aaravjhamb/zhifubao/assets/41279.jpg

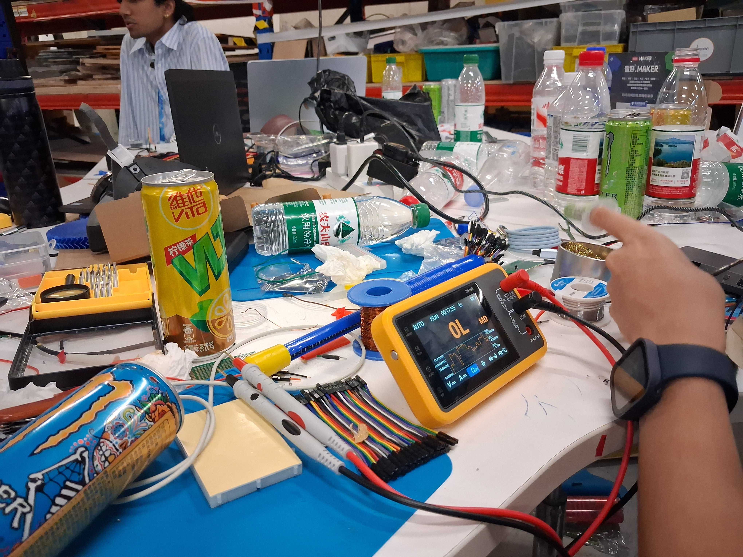
assets/41279.jpg
