aaravjhamb/zhifubao/hardware/zhifubros.kicad_sch

## KiCad design hardware/zhifubros.kicad_sch (2026-07-06, an earlier design)

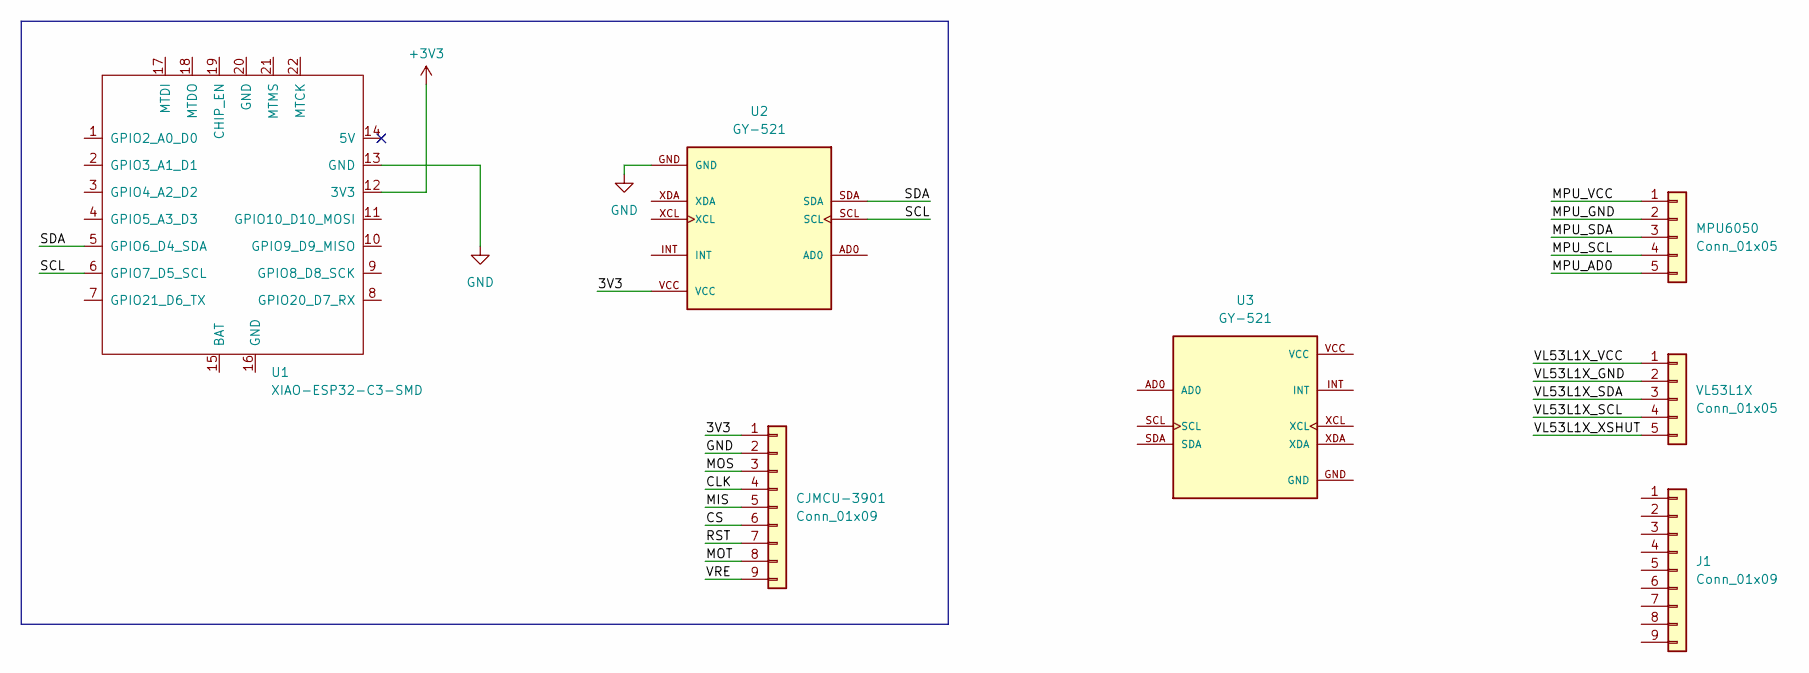
[picture p15: schematic zhifubros.kicad_sch]

Parts:
CJMCU-3901: Conn_01x09
J1: Conn_01x09
MPU6050: Conn_01x05
U1: XIAO-ESP32-C3-SMD
U2, U3: GY-521; MODULE_GY-521; PARTREV NA
VL53L1X: Conn_01x05

Connections:
3V3: CJMCU-3901.1, U2.VCC
+3V3: U1.12 (3V3)
CLK: CJMCU-3901.4
CS: CJMCU-3901.6
GND: CJMCU-3901.2, U1.13 (GND), U2.GND
MIS: CJMCU-3901.5
MOS: CJMCU-3901.3
MOT: CJMCU-3901.8
MPU_AD0: MPU6050.5
MPU_GND: MPU6050.2
MPU_SCL: MPU6050.4
MPU_SDA: MPU6050.3
MPU_VCC: MPU6050.1
RST: CJMCU-3901.7
SCL: U1.6 (GPIO7_D5_SCL), U2.SCL
SDA: U1.5 (GPIO6_D4_SDA), U2.SDA
VL53L1X_GND: VL53L1X.2
VL53L1X_SCL: VL53L1X.4
VL53L1X_SDA: VL53L1X.3
VL53L1X_VCC: VL53L1X.1
VL53L1X_XSHUT: VL53L1X.5
VRE: CJMCU-3901.9
