aaravjhamb/zhifubao/assets/41325.jpg

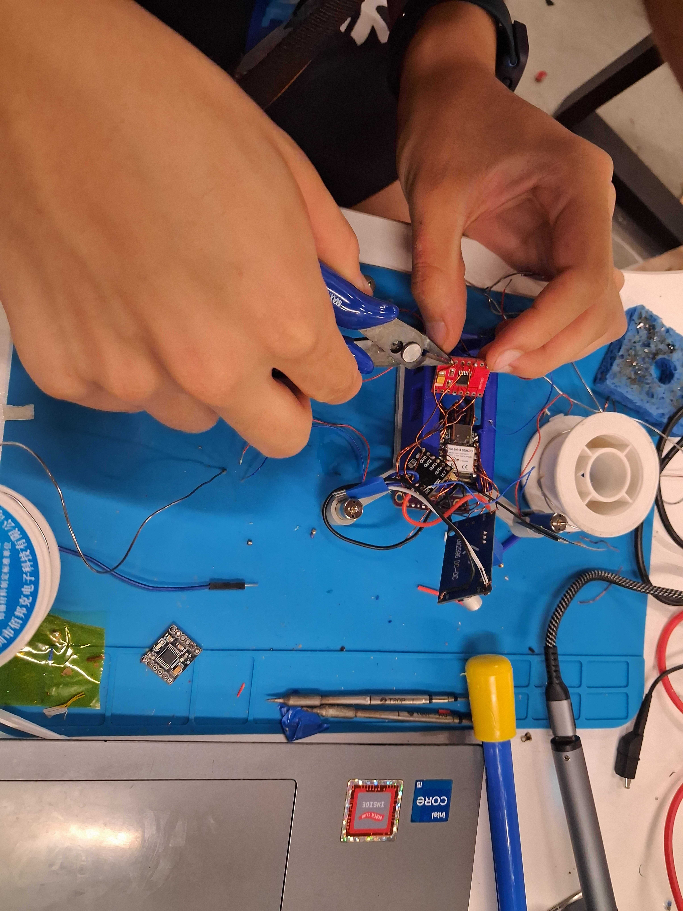
assets/41325.jpg
