aaravjhamb/zhifubao/assets/41326.jpg

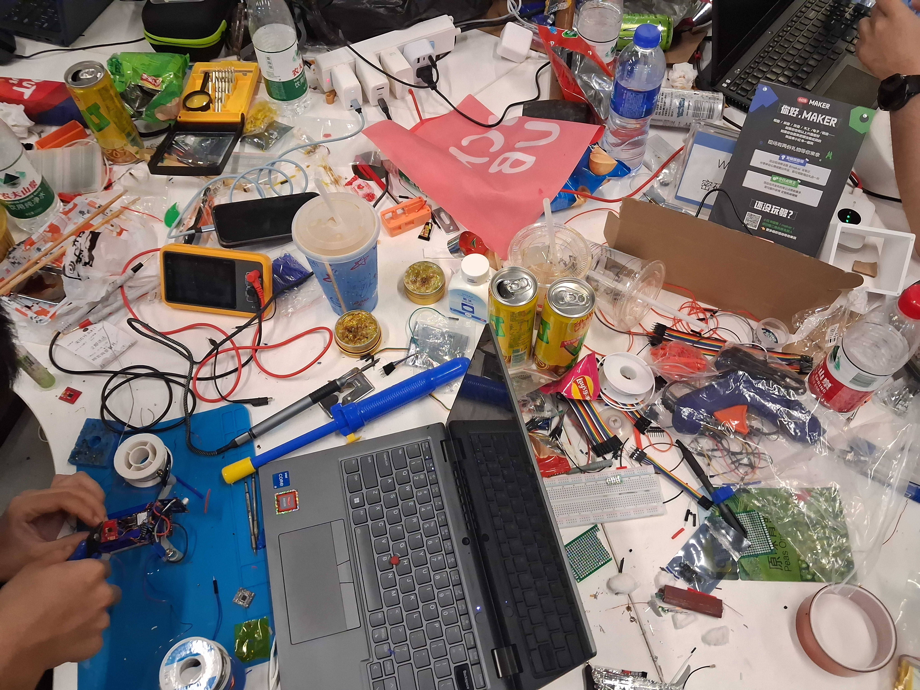
assets/41326.jpg
